twy2020/Handheld-spectrometer/pic/3D.png

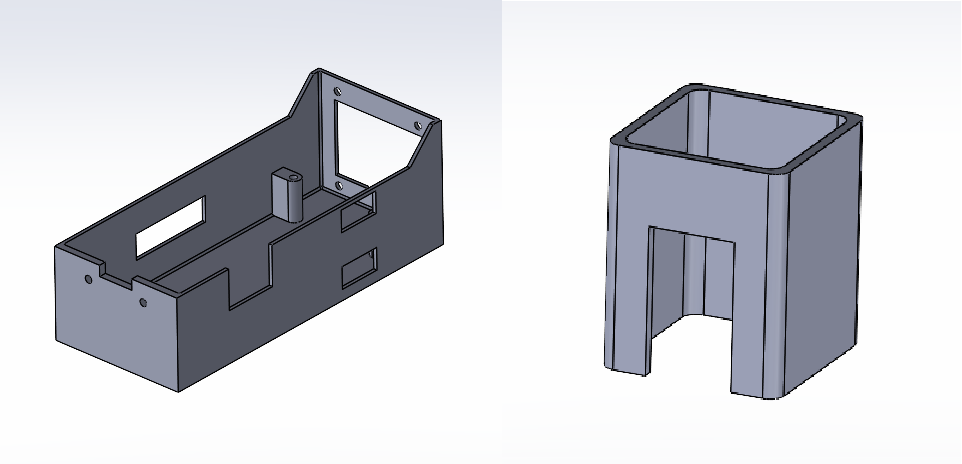
pic/3D.png
