twy2020/Handheld-spectrometer/pic/bat.jpg

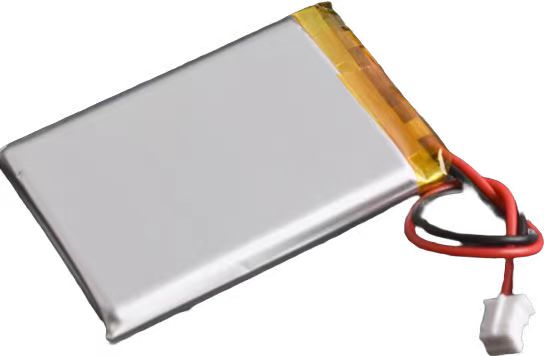
pic/bat.jpg
