twy2020/Handheld-spectrometer/pic/data.jpg

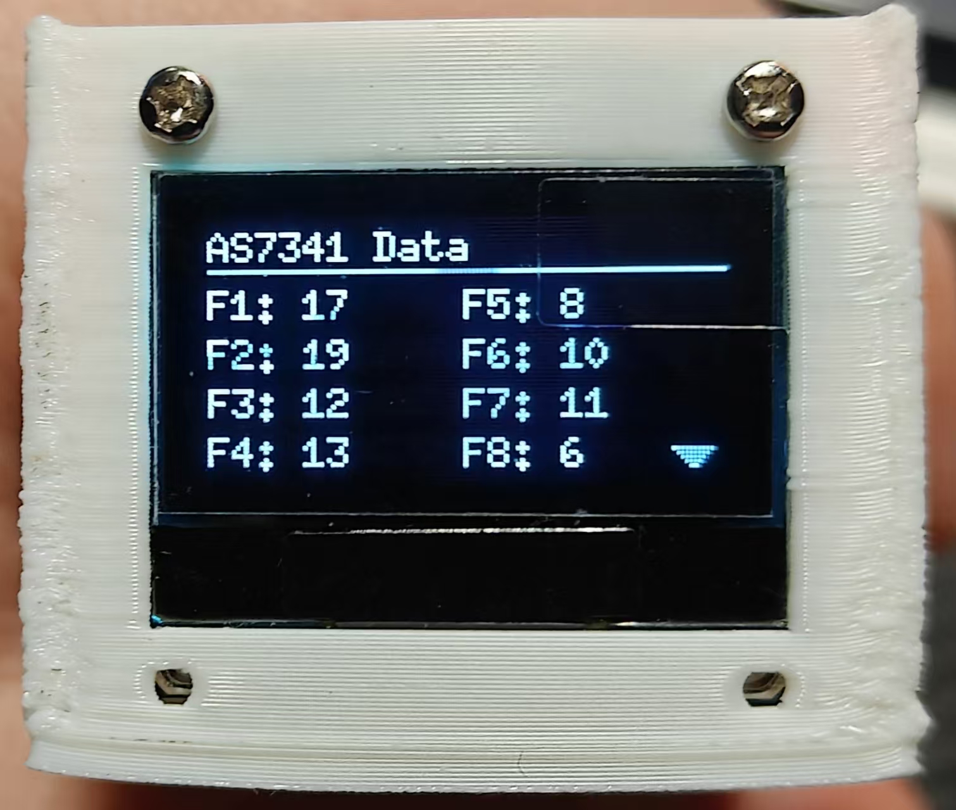
pic/data.jpg
