twy2020/Handheld-spectrometer/pic/ESP32C3_Super_Mini.png

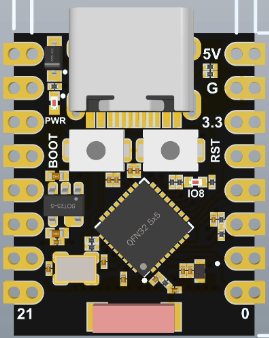
pic/ESP32C3_Super_Mini.png
