twy2020/Handheld-spectrometer/pic/head.png

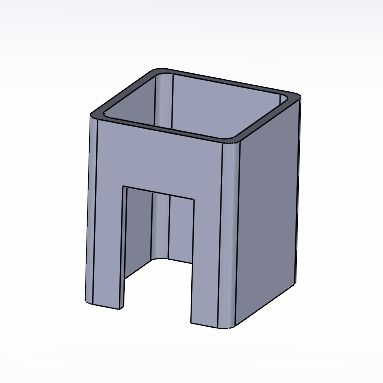
pic/head.png
