twy2020/Handheld-spectrometer/pic/key.jpg

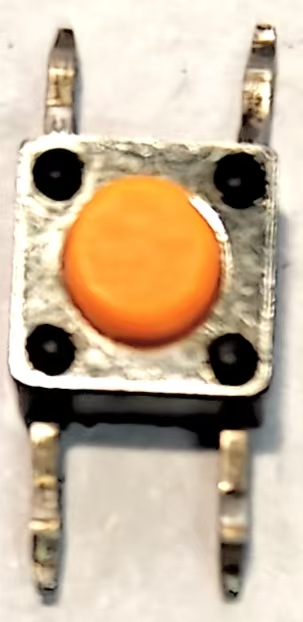
pic/key.jpg
