twy2020/Handheld-spectrometer/pic/LED_driver_board.jpg

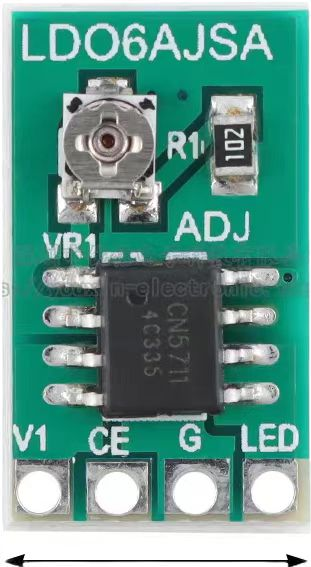
pic/LED_driver_board.jpg
