twy2020/Handheld-spectrometer/pic/li_charge_discharge_modul.jpg

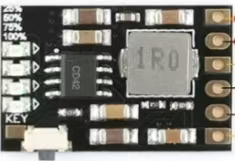
pic/li_charge_discharge_modul.jpg
