twy2020/Handheld-spectrometer/pic/OLED.png

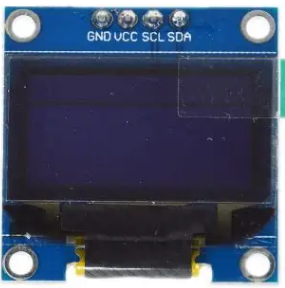
pic/OLED.png
