twy2020/Handheld-spectrometer/pic/PC_1.png

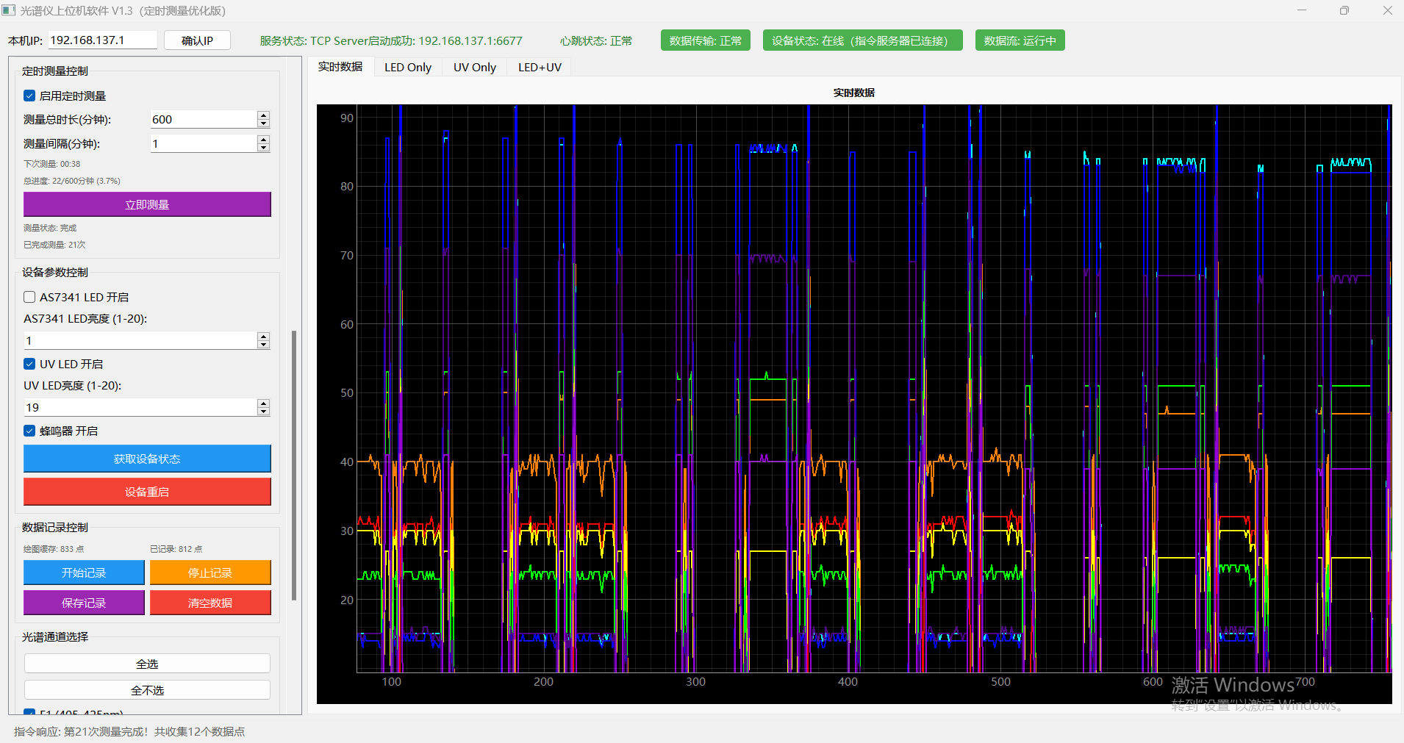
pic/PC_1.png
