twy2020/Handheld-spectrometer/pic/RFRobot_AS7341.jpg

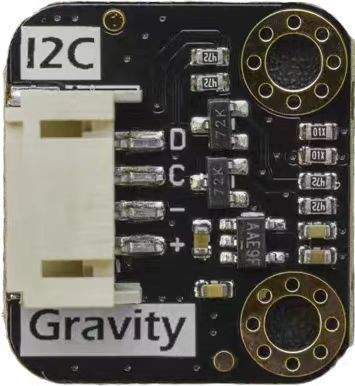
pic/RFRobot_AS7341.jpg
