twy2020/Handheld-spectrometer/pic/switch.png

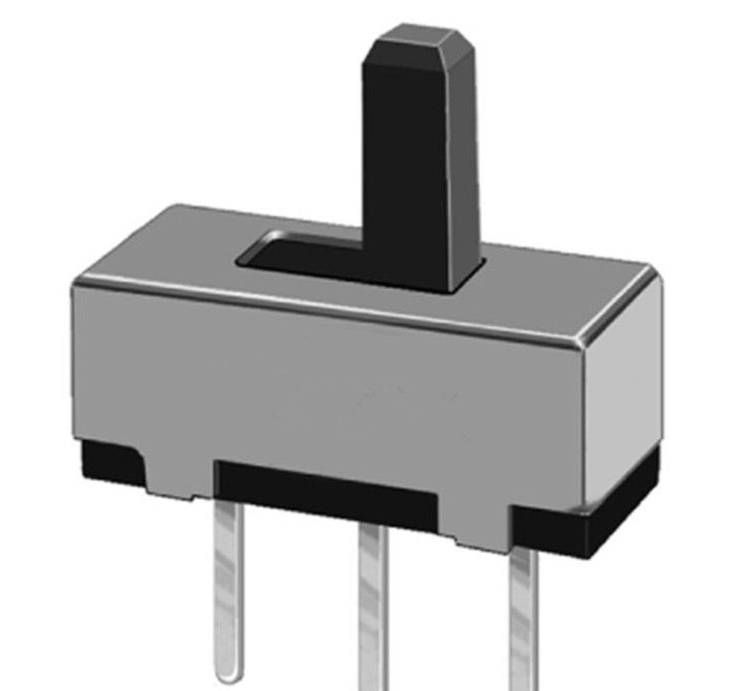
pic/switch.png
