twy2020/Handheld-spectrometer/pic/type-c_charge_modul.jpg

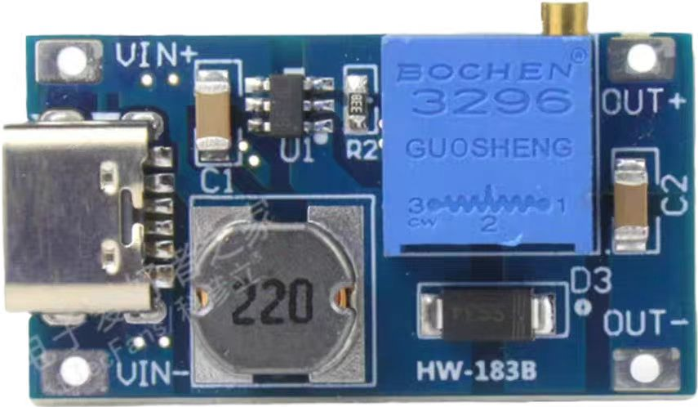
pic/type-c_charge_modul.jpg
