twy2020/Handheld-spectrometer/pic/UV_LED_365nm_5mm.jpg

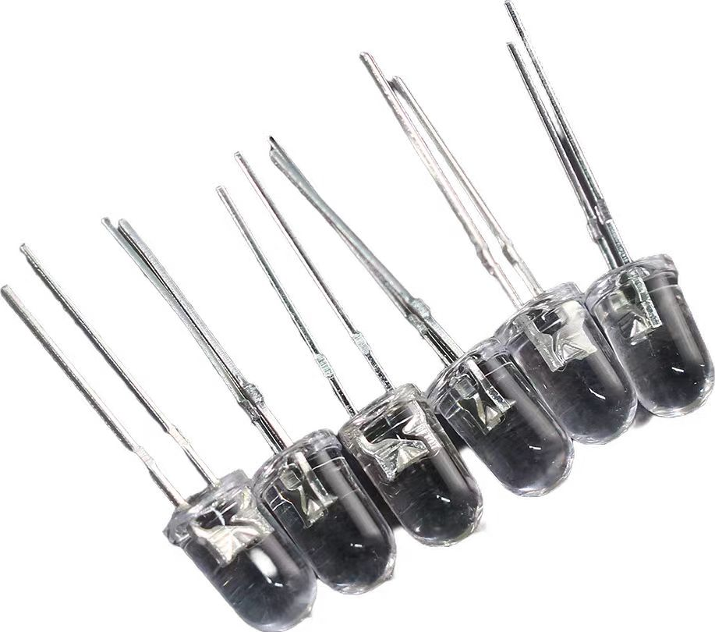
pic/UV_LED_365nm_5mm.jpg
