twy2020/Handheld-spectrometer/pic/work_1.jpg

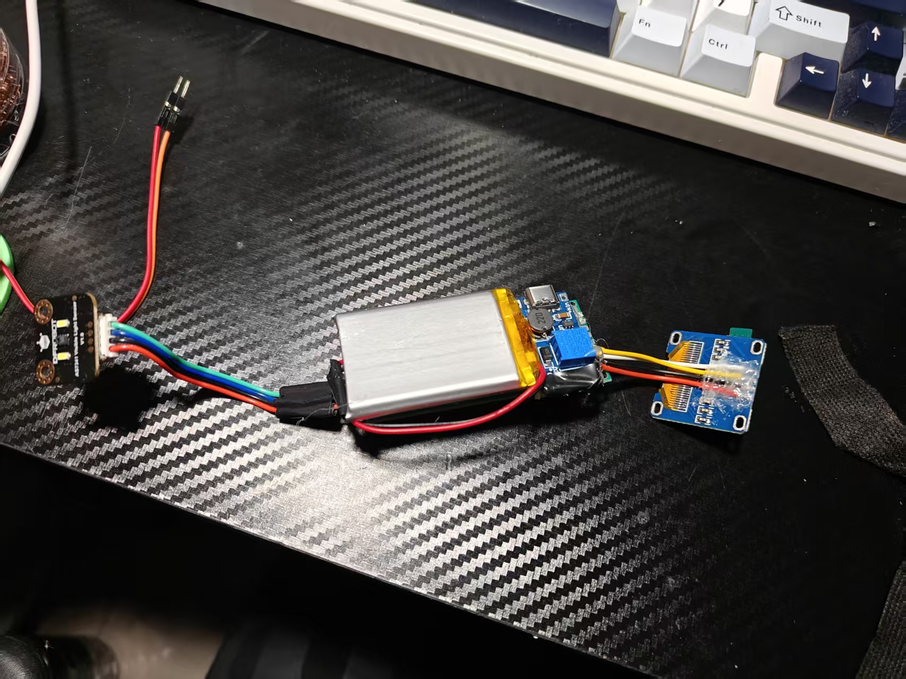
pic/work_1.jpg
