twy2020/Handheld-spectrometer/pic/work_2.jpg

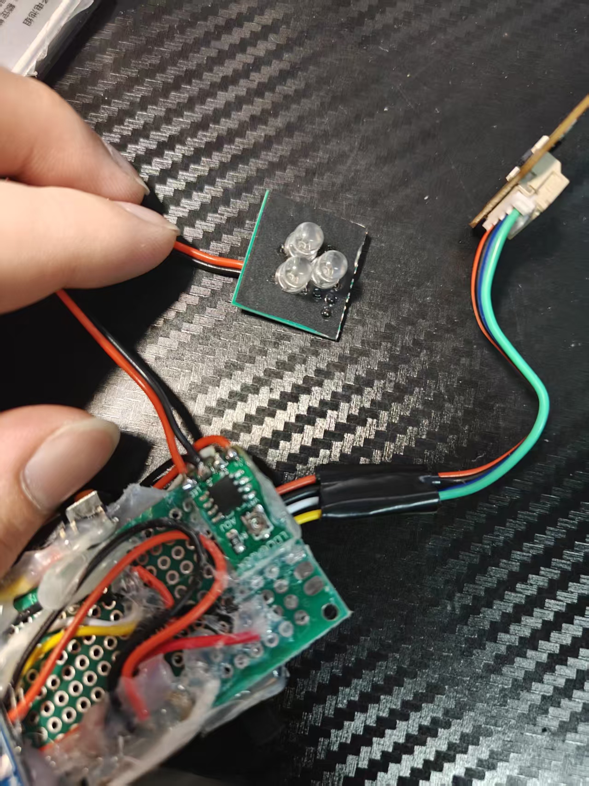
pic/work_2.jpg
