twy2020/Handheld-spectrometer/pic/work_3.jpg

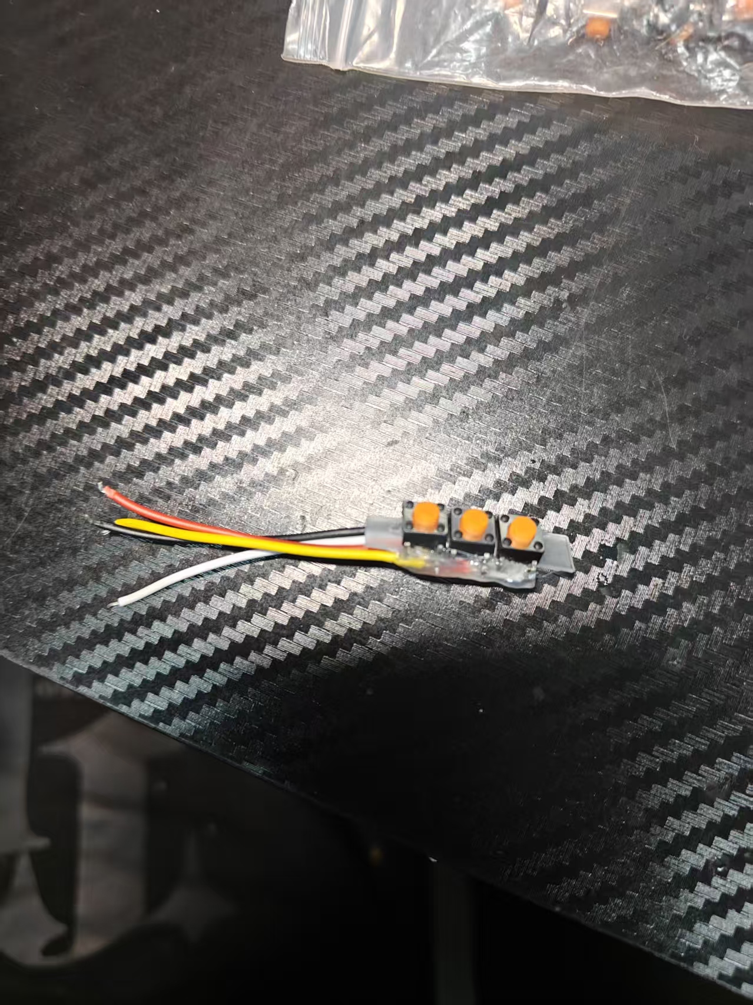
pic/work_3.jpg
