twy2020/Handheld-spectrometer/pic/work_4.jpg

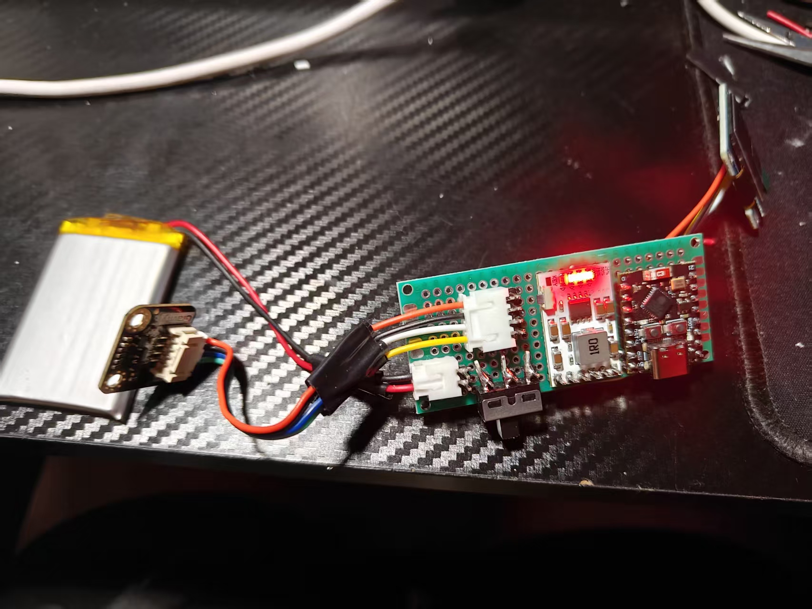
pic/work_4.jpg
