twy2020/Handheld-spectrometer/pic/work_5.jpg

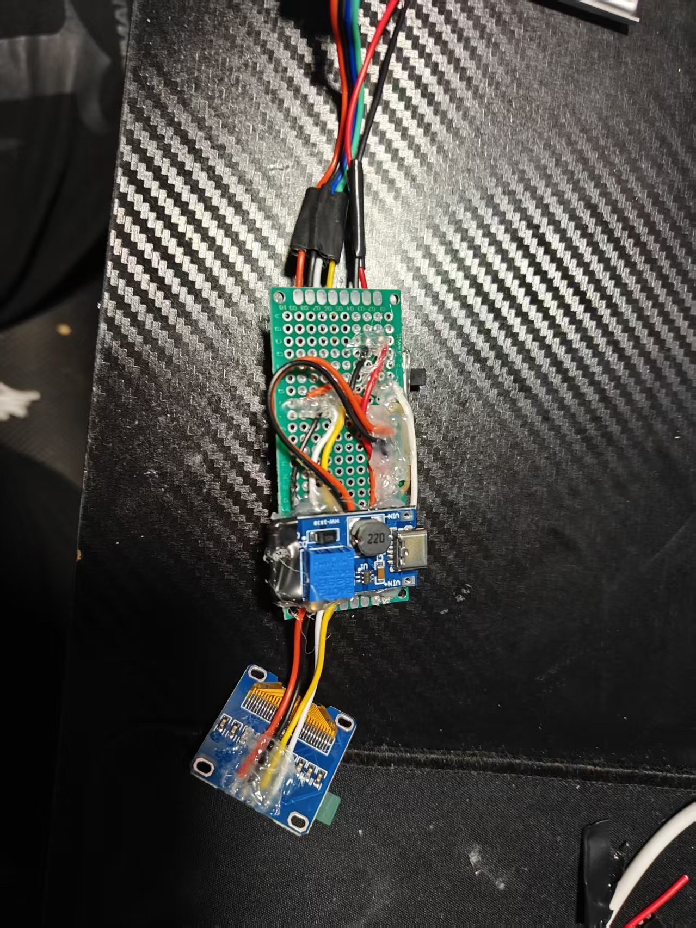
pic/work_5.jpg
