twy2020/Handheld-spectrometer/pic/work_6.jpg

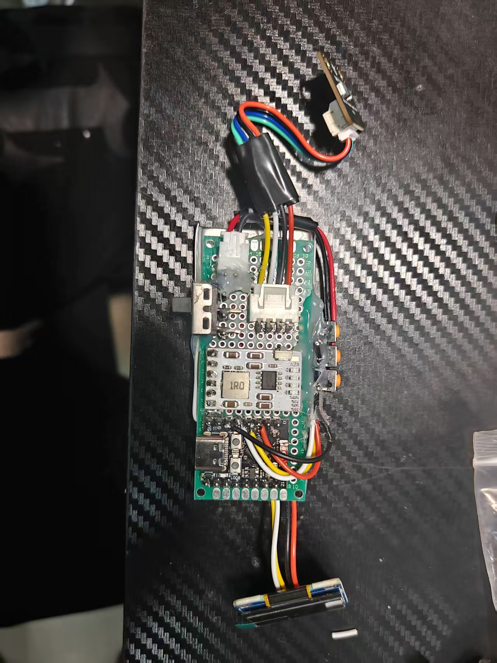
pic/work_6.jpg
