twy2020/Handheld-spectrometer/pic/work_7.jpg

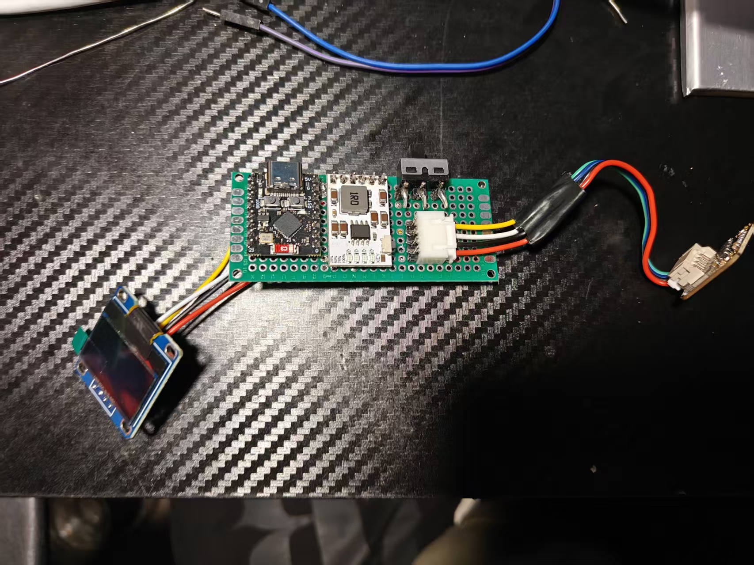
pic/work_7.jpg
