twy2020/Handheld-spectrometer/pic/work_9.jpg

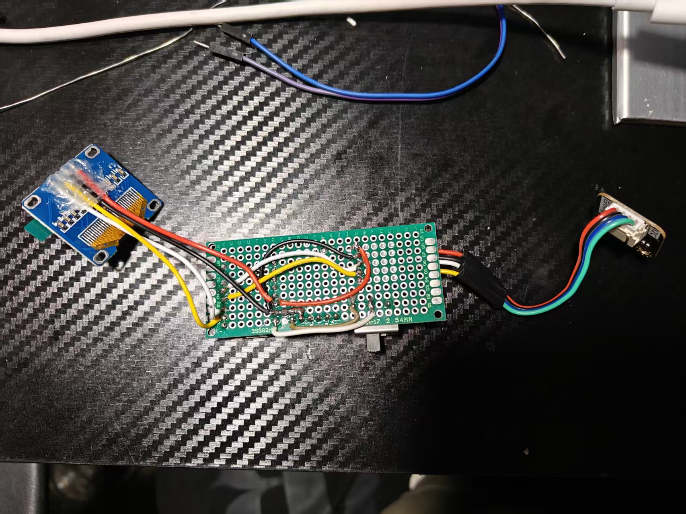
pic/work_9.jpg
