twy2020/Handheld-spectrometer/pic/work_10.jpg

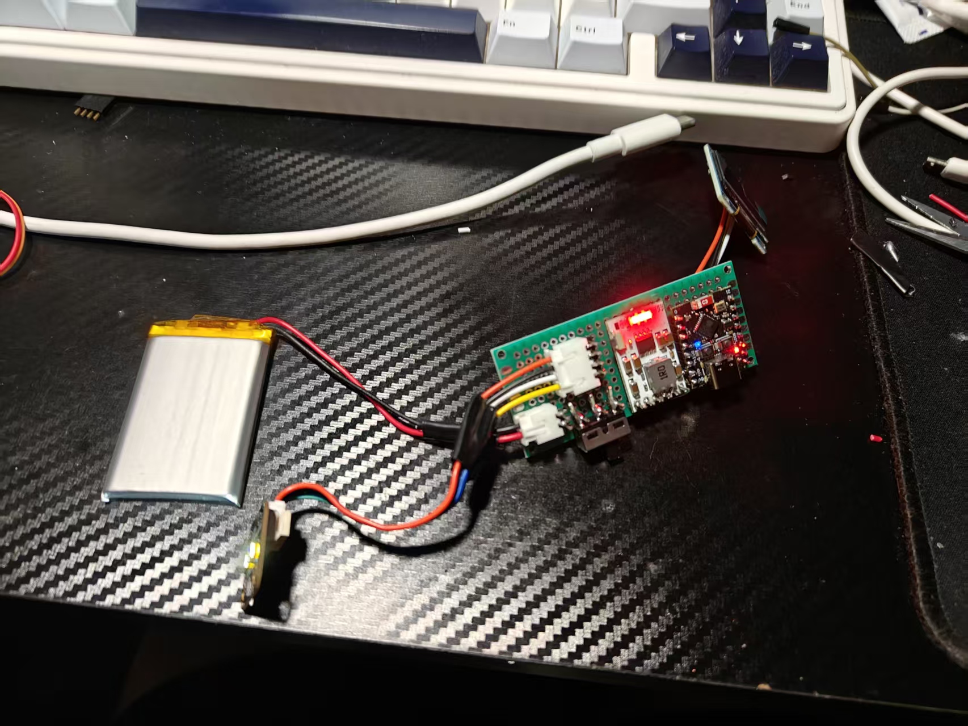
pic/work_10.jpg
