twy2020/Handheld-spectrometer/pic/work_11.jpg

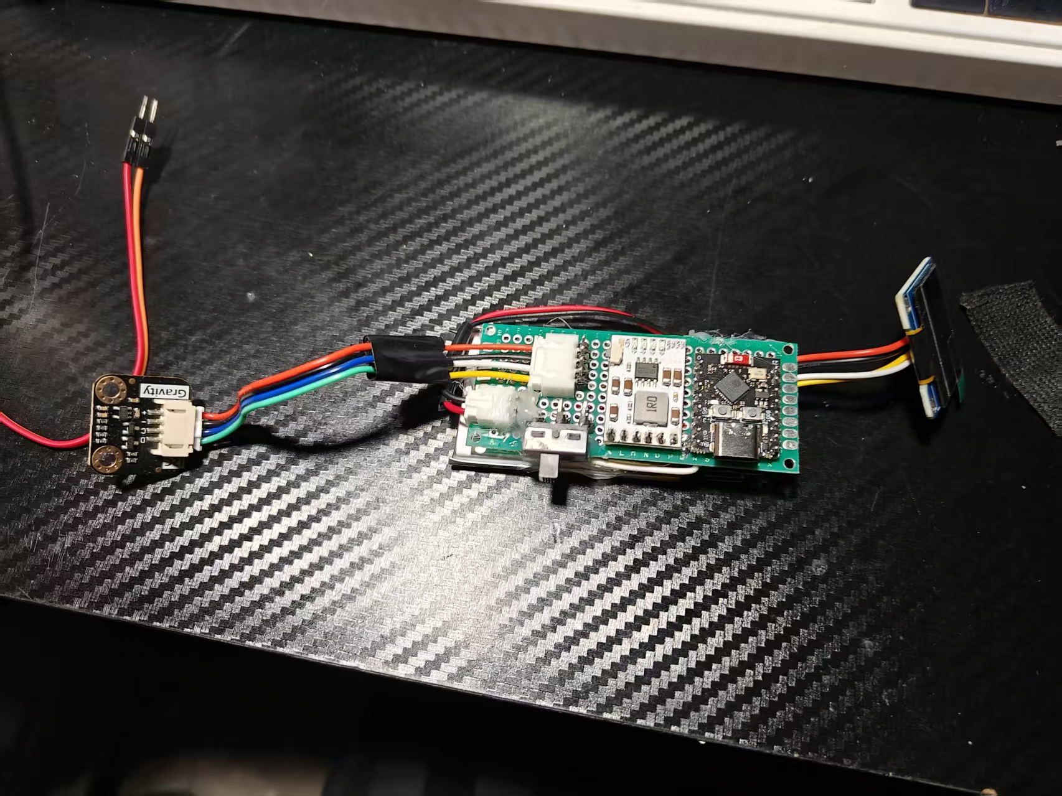
pic/work_11.jpg
