twy2020/Handheld-spectrometer/pic/test_3.jpg

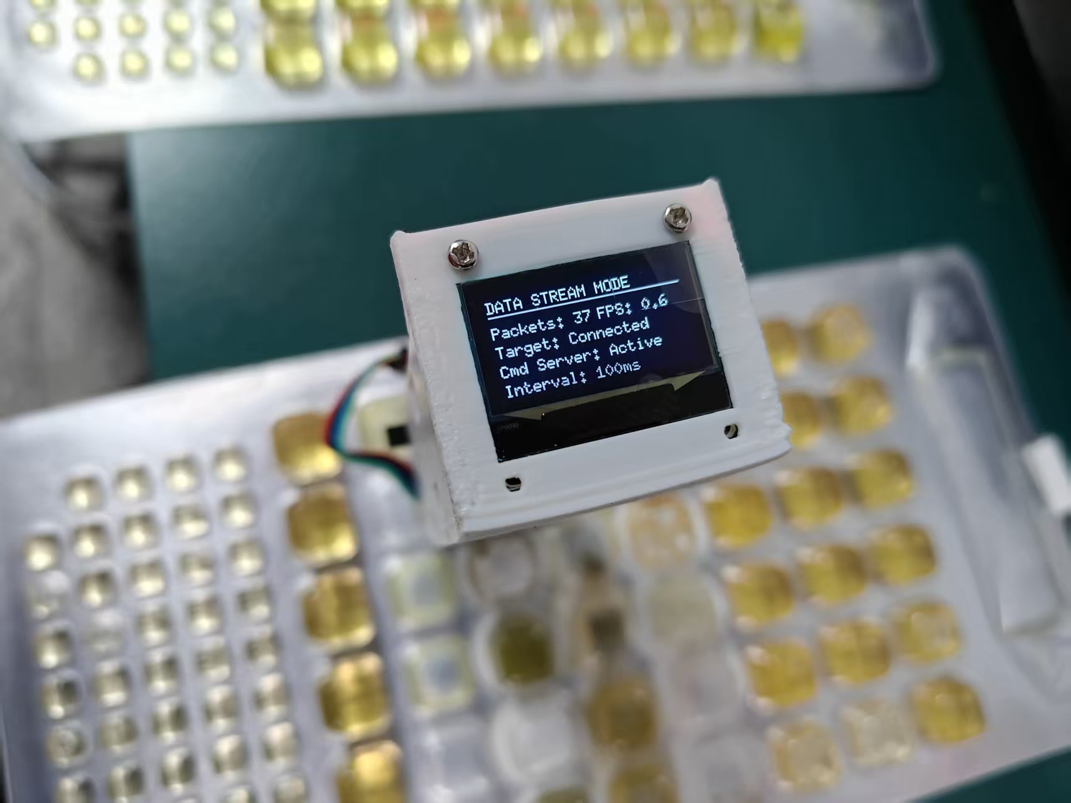
pic/test_3.jpg
