twy2020/Handheld-spectrometer/sample_data/result.png

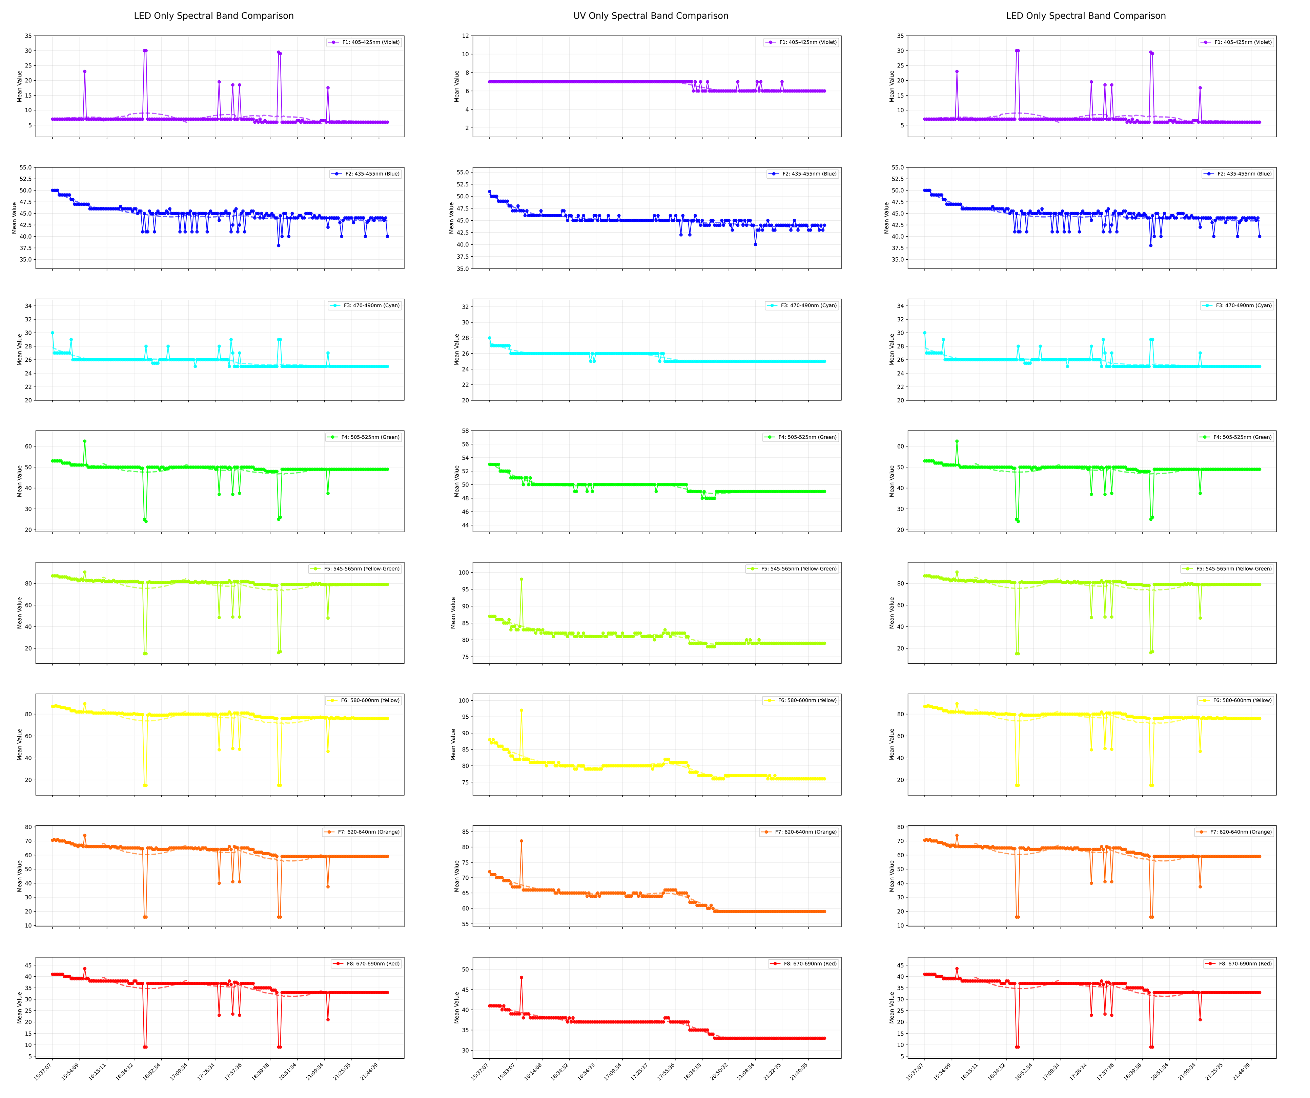
sample_data/result.png
